nearestexit/mx-unsaver/USBHubV3/USBHubV3.step

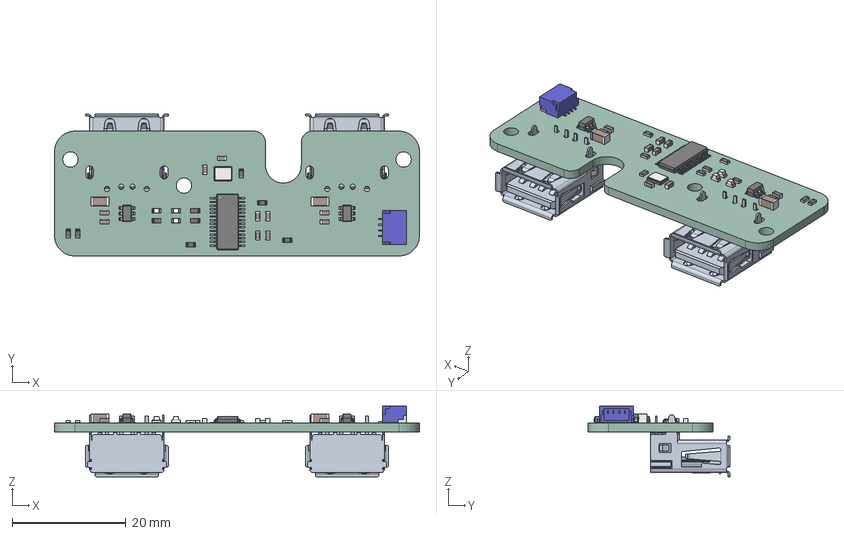
[picture p17: CAD file, 2026-01-19]
USBHubV3/USBHubV3.step
64.3 x 25.0 x 12.5 mm
R_0603_1608Metric x 9
C_0603_1608Metric x 10
Crystal_SMD_3225-4Pin_3.2x2.5mm
SSOP_28_39x99mm_P0635mm
SOT_23_6 x 2
C_1206_3216Metric x 2
SM04B-SRSS
LED_0603_1608Metric x 3
C-6364372-2 x 2
USBHubV3_PCB
