nearestexit/mx-unsaver/Case/STEP/Bottom Case.step

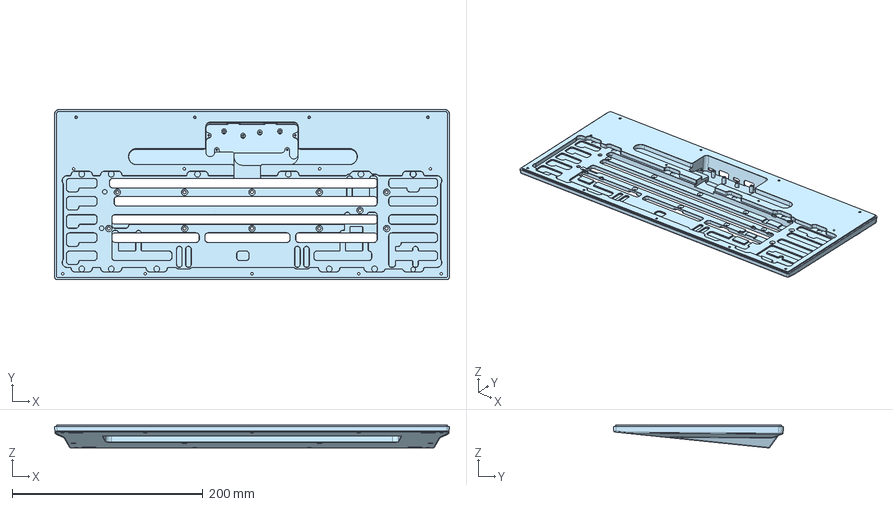
[picture p18: CAD file, 2026-01-19]
Case/STEP/Bottom Case.step
414.4 x 178.6 x 24.1 mm
