nearestexit/mx-unsaver/mx-unsaver-frow/F-Row PCB Layout.dxf

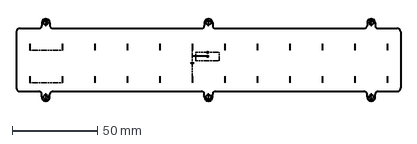
[picture p19: CAD file, 2026-01-19]
mx-unsaver-frow/F-Row PCB Layout.dxf
225.2 x 48.3 mm
