nearestexit/mx-unsaver/mx-unsaver-main/Drawing - LShift.dxf

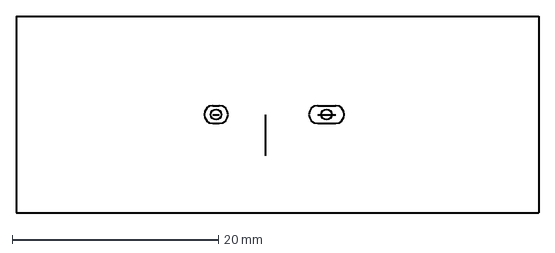
[picture p20: CAD file, 2026-01-19]
mx-unsaver-main/Drawing - LShift.dxf
50.6 x 19.1 mm
