nearestexit/mx-unsaver/mx-unsaver-numpad/mx-unsaver-numpad.step

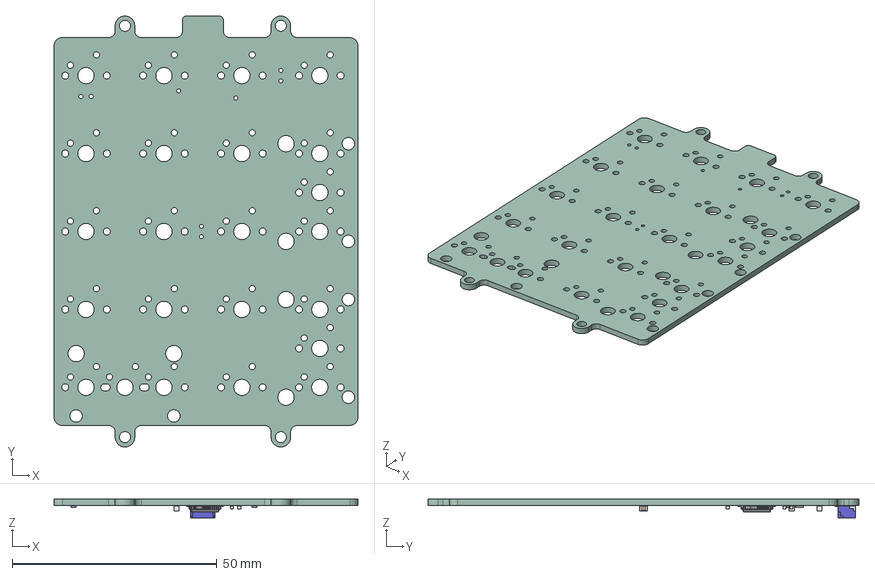
[picture p21: CAD file, 2026-01-19]
mx-unsaver-numpad/mx-unsaver-numpad.step
74.3 x 105.4 x 4.61 mm
R_0805_2012Metric x 2
C_0805_2012Metric x 3
C_0603_1608Metric x 6
LQFP_48_7x7mm_P05mm
SM04B-SRSS
mx-unsaver-numpad_PCB
