nearestexit/mx-unsaver/Numpad_Daughterboard/Numpad DB Layout.dxf

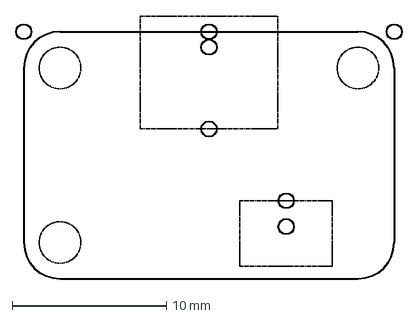
[picture p22: CAD file, 2026-01-19]
Numpad_Daughterboard/Numpad DB Layout.dxf
25.0 x 17.0 mm
