nearestexit/mx-unsaver/USBHubV3/USB-A PCB Edge.Cuts.dxf

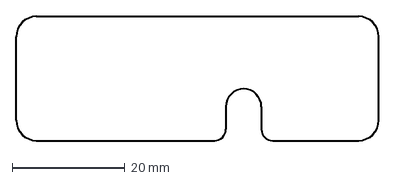
[picture p23: CAD file, 2026-01-19]
USBHubV3/USB-A PCB Edge.Cuts.dxf
64.3 x 22.0 mm
