nearestexit/mx-unsaver/Case/STEP/Bottom Case - Numpad.step

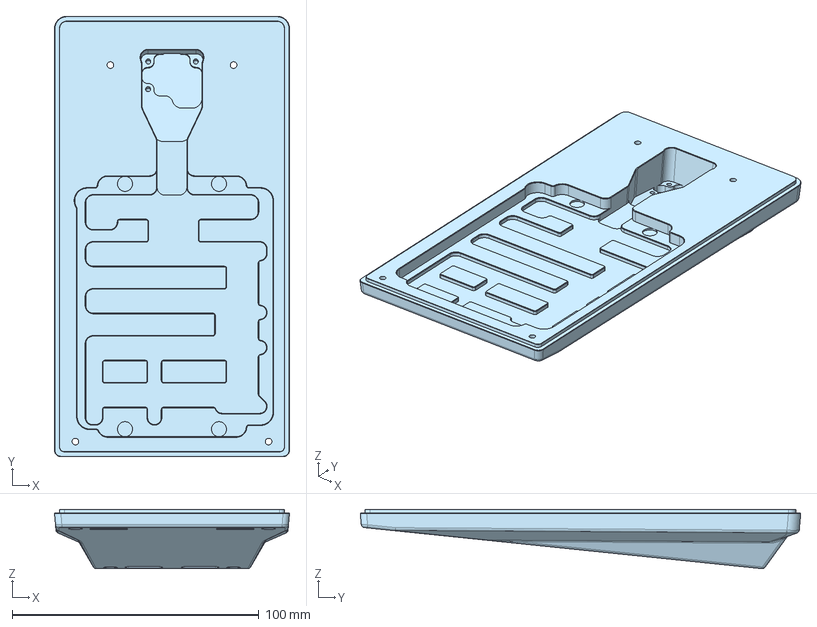
[picture p24: CAD file, 2026-01-19]
Case/STEP/Bottom Case - Numpad.step
95.3 x 178.6 x 24.1 mm
