nearestexit/mx-unsaver/mx-unsaver-main/Drawing - Enter.dxf

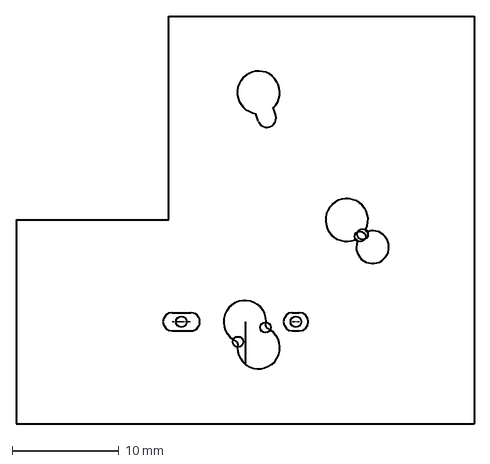
[picture p25: CAD file, 2026-01-19]
mx-unsaver-main/Drawing - Enter.dxf
42.9 x 38.1 mm
