nearestexit/mx-unsaver/Case/STEP/Top Case.step

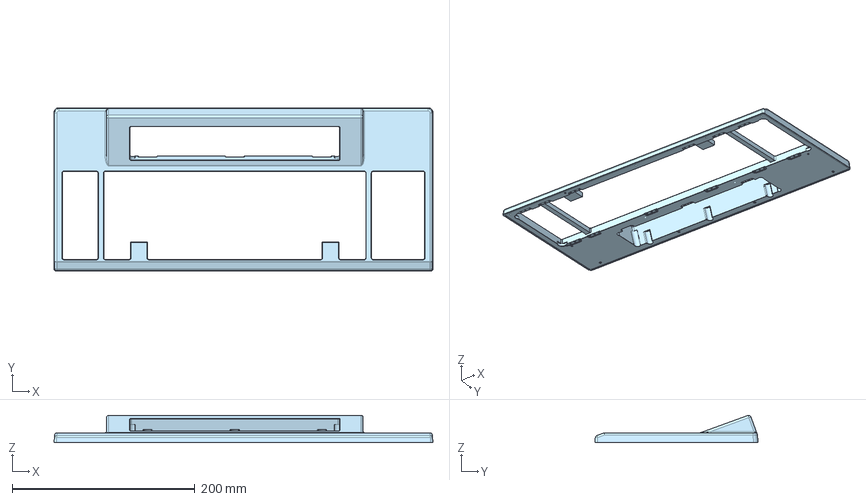
[picture p26: CAD file, 2026-01-19]
Case/STEP/Top Case.step
414.4 x 178.6 x 30.0 mm
