nearestexit/mx-unsaver/mx-unsaver-main/Drawing - Split Backspace Slots.dxf

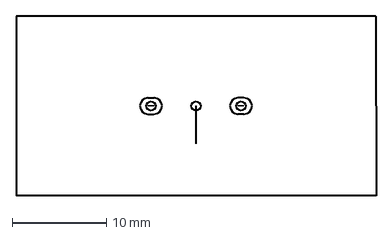
[picture p27: CAD file, 2026-01-19]
mx-unsaver-main/Drawing - Split Backspace Slots.dxf
38.1 x 19.0 mm
