nearestexit/mx-unsaver/Case/STEP/Top Case - Numpad.step

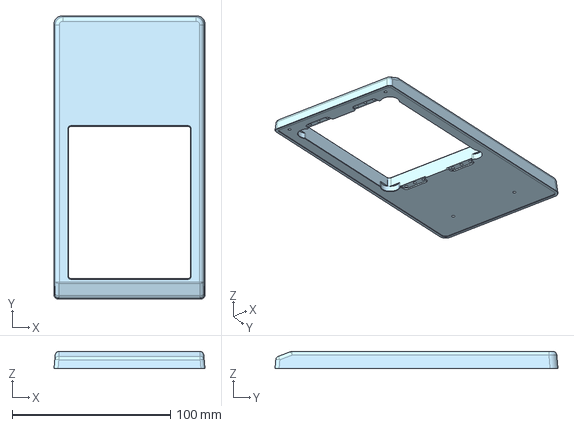
[picture p28: CAD file, 2026-01-19]
Case/STEP/Top Case - Numpad.step
95.3 x 178.6 x 10.9 mm
