nearestexit/mx-unsaver/mx-unsaver-main/PCB Edge.cuts.dxf

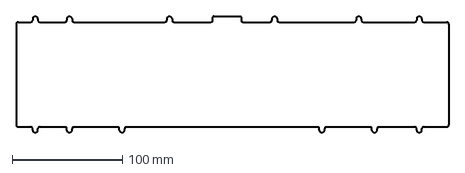
[picture p29: CAD file, 2026-01-19]
mx-unsaver-main/PCB Edge.cuts.dxf
391.8 x 105.4 mm
