nearestexit/mx-unsaver/Case/STEP/Weight.step

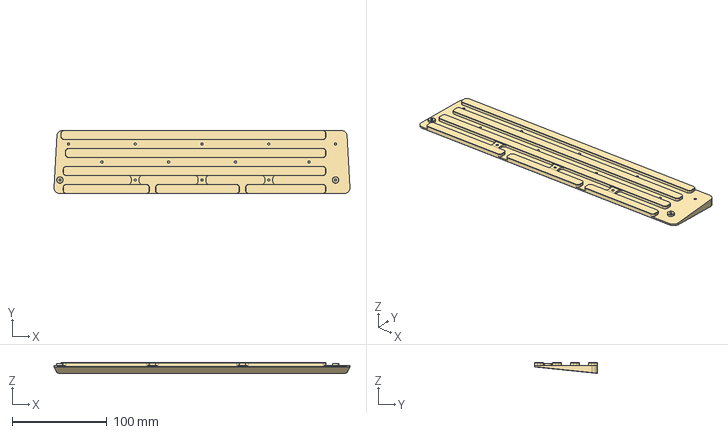
[picture p30: CAD file, 2026-01-19]
Case/STEP/Weight.step
313.1 x 66.7 x 11.5 mm
